SeeedDocument/BeagleBone_Green/bbg12.png

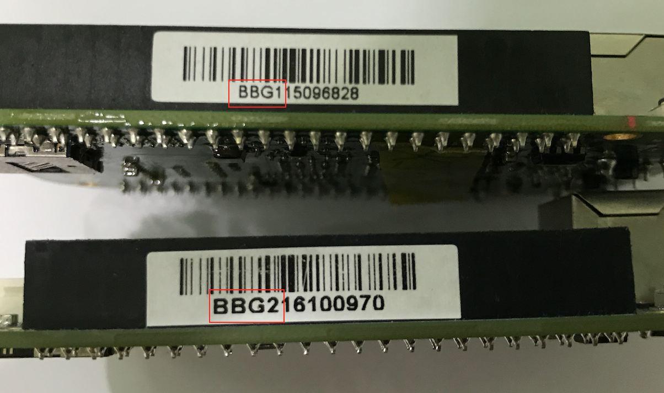
bbg12.png
