SeeedDocument/BeagleBone_Green/images/BBG_drawing_1.png

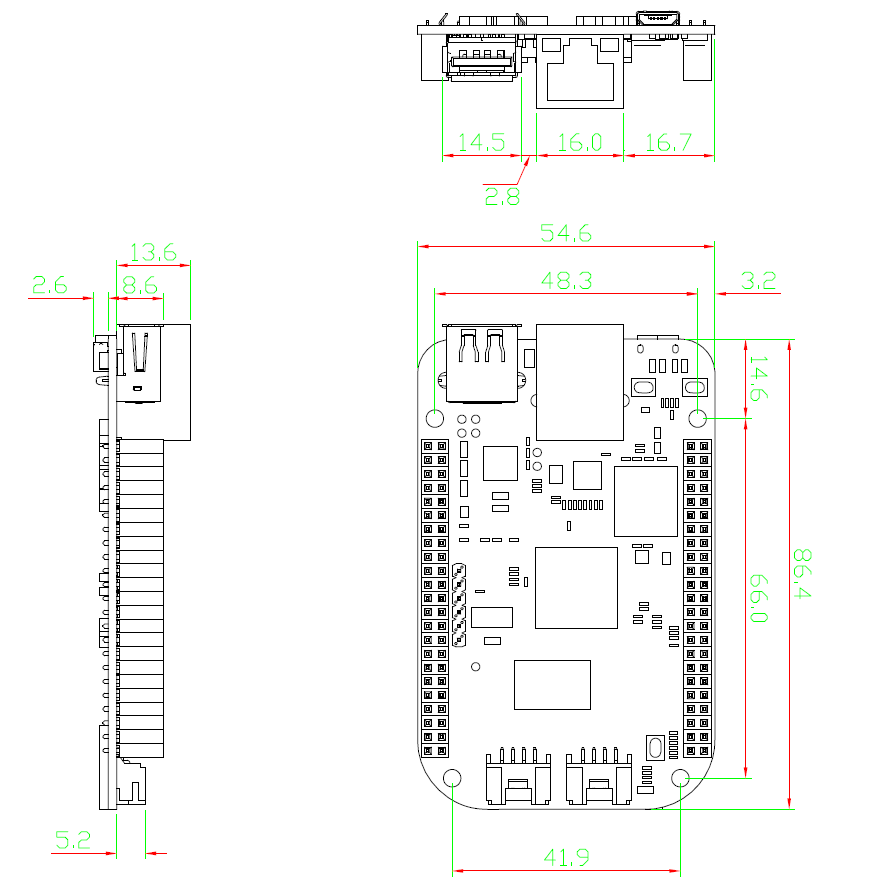
images/BBG_drawing_1.png
