SeeedDocument/BeagleBone_Green/images/win32_disk_image_confirm.png

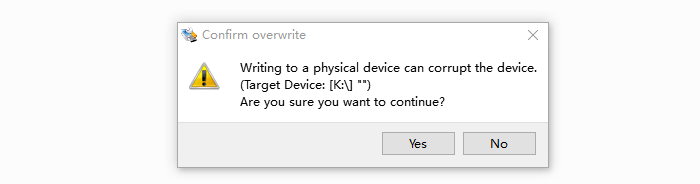
images/win32_disk_image_confirm.png
